arvjus/FileStorage_RC6502_Apple1/software/firmware/defs.h

/*
RC6502 FLASH (W25Q64F) Card firmware
Copyright (c) 2025 Arvid Juskaitis
*/

#pragma once

// disable parts in order to fit with bootloader
#define BULK_TRANSFER   1
#define LIST            1
#define READ            1
#define WRITE           1
#define DELETE          1
#define UNUSED          0
